rainad33r/BiomechanicalWheat2025/CollectedData/MaterialTesting/CrossSectionImages/D105.jpg

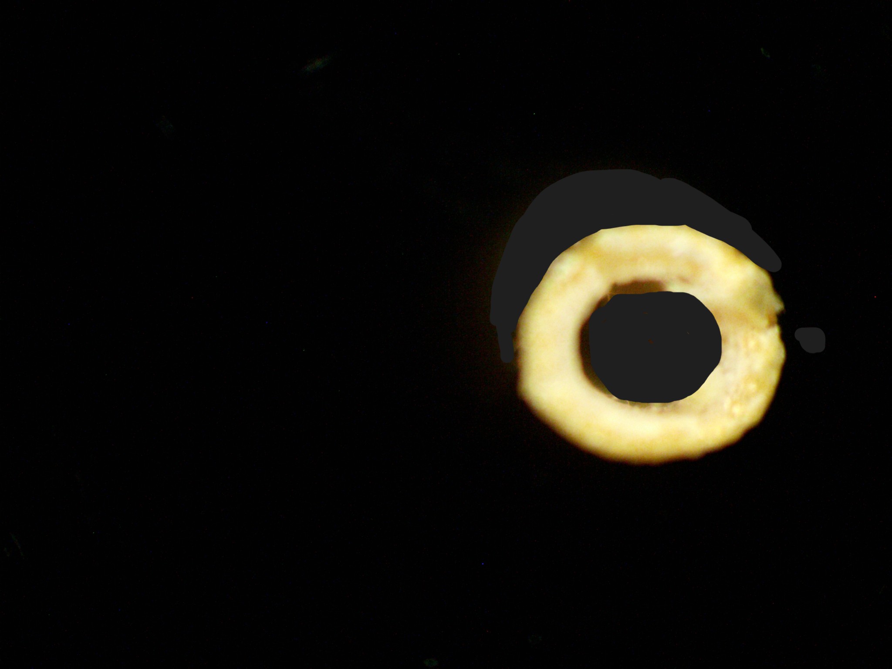
CollectedData/MaterialTesting/CrossSectionImages/D105.jpg
