rainad33r/BiomechanicalWheat2025/CollectedData/MaterialTesting/CrossSectionImages/D160.jpg

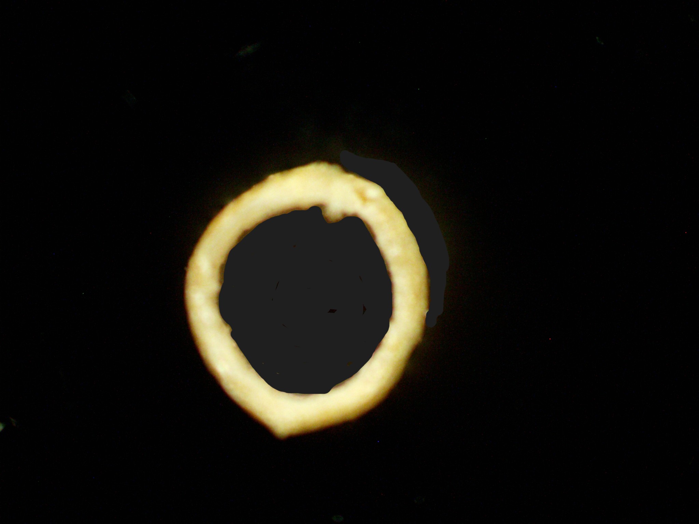
CollectedData/MaterialTesting/CrossSectionImages/D160.jpg
