rainad33r/BiomechanicalWheat2025/CollectedData/MaterialTesting/CrossSectionImages/L15.jpg

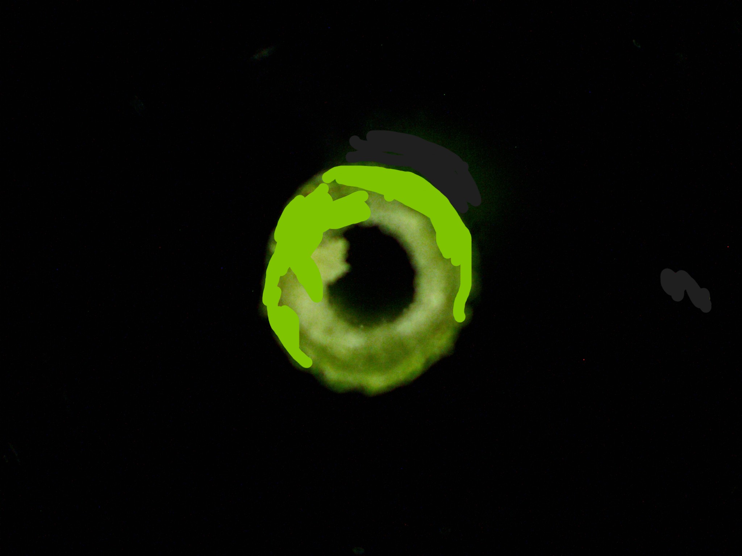
CollectedData/MaterialTesting/CrossSectionImages/L15.jpg
