rainad33r/BiomechanicalWheat2025/CollectedData/MaterialTesting/CrossSectionImages/L100.jpg

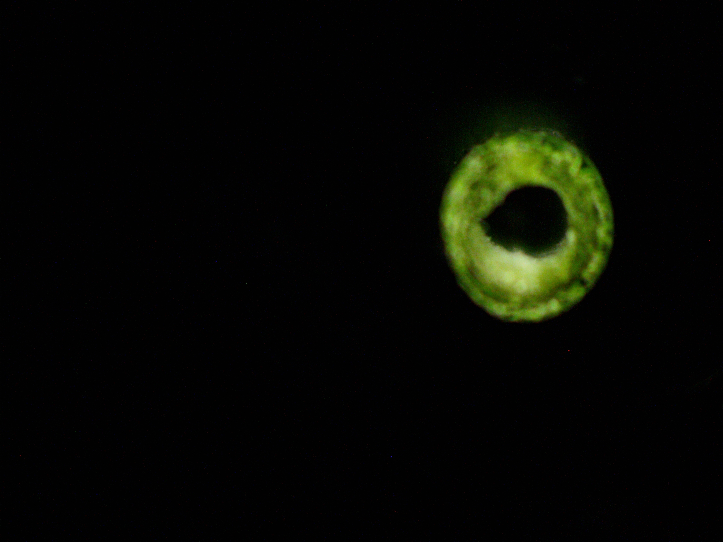
CollectedData/MaterialTesting/CrossSectionImages/L100.jpg
