rainad33r/BiomechanicalWheat2025/CollectedData/MaterialTesting/CrossSectionImages/L144.jpg

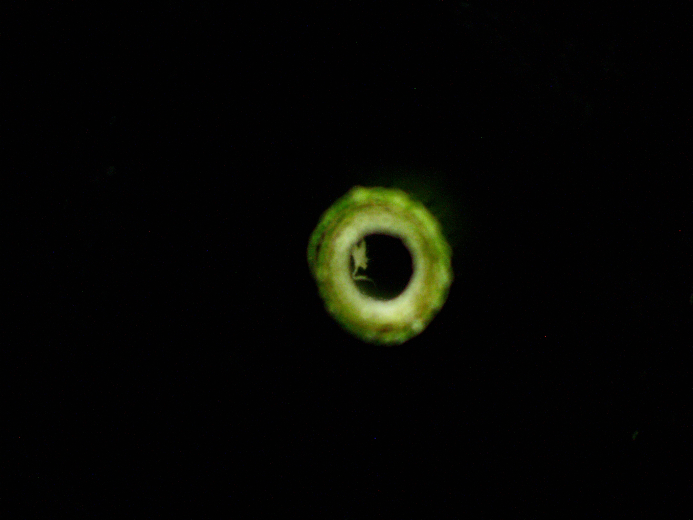
CollectedData/MaterialTesting/CrossSectionImages/L144.jpg
