rainad33r/BiomechanicalWheat2025/CollectedData/MaterialTesting/CrossSectionImages/L183.jpg

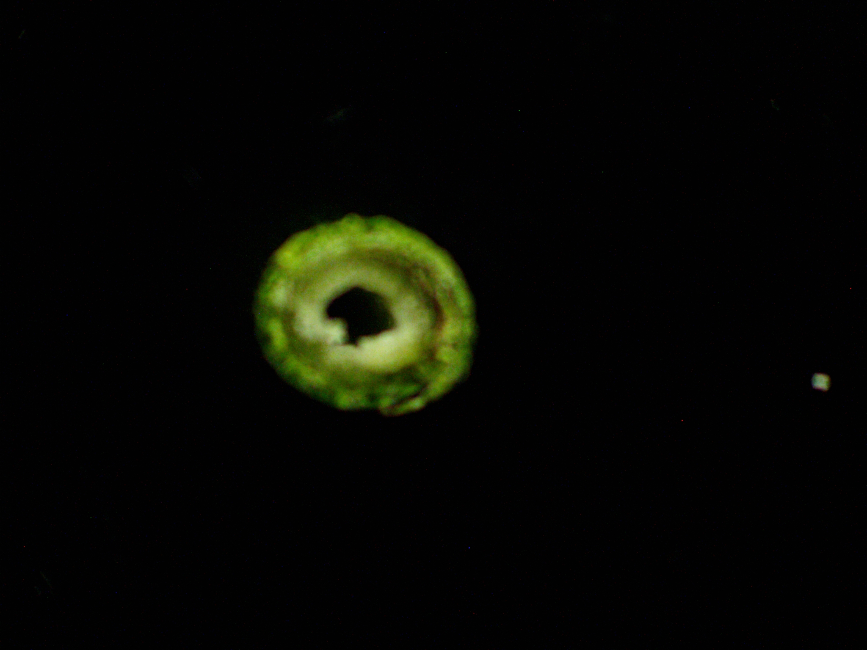
CollectedData/MaterialTesting/CrossSectionImages/L183.jpg
